FutilityDesigns/Glyph-Reader/Firmware/images/dark.bmp

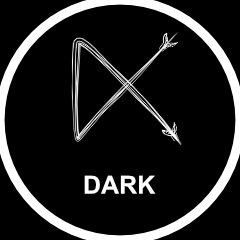
Firmware/images/dark.bmp
