FutilityDesigns/Glyph-Reader/Firmware/images/Gust.bmp

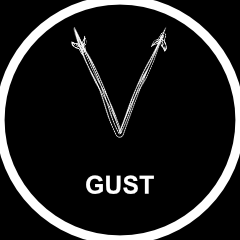
Firmware/images/Gust.bmp
