FutilityDesigns/Glyph-Reader/Firmware/images/halt.bmp

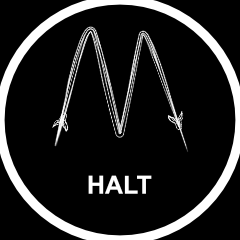
Firmware/images/halt.bmp
