FutilityDesigns/Glyph-Reader/Firmware/images/ignite.bmp

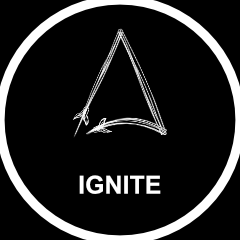
Firmware/images/ignite.bmp
