FutilityDesigns/Glyph-Reader/Firmware/images/lower.bmp

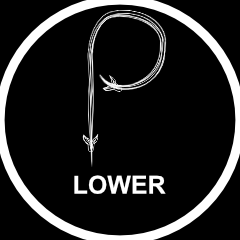
Firmware/images/lower.bmp
