FutilityDesigns/Glyph-Reader/Firmware/images/raise.bmp

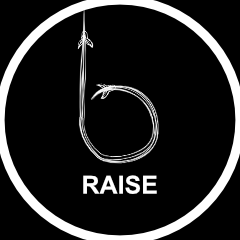
Firmware/images/raise.bmp
