FutilityDesigns/Glyph-Reader/Firmware/images/unlock.bmp

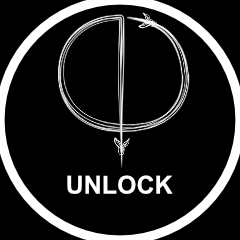
Firmware/images/unlock.bmp
