FutilityDesigns/Glyph-Reader/Spell Cheat Sheet.jpg

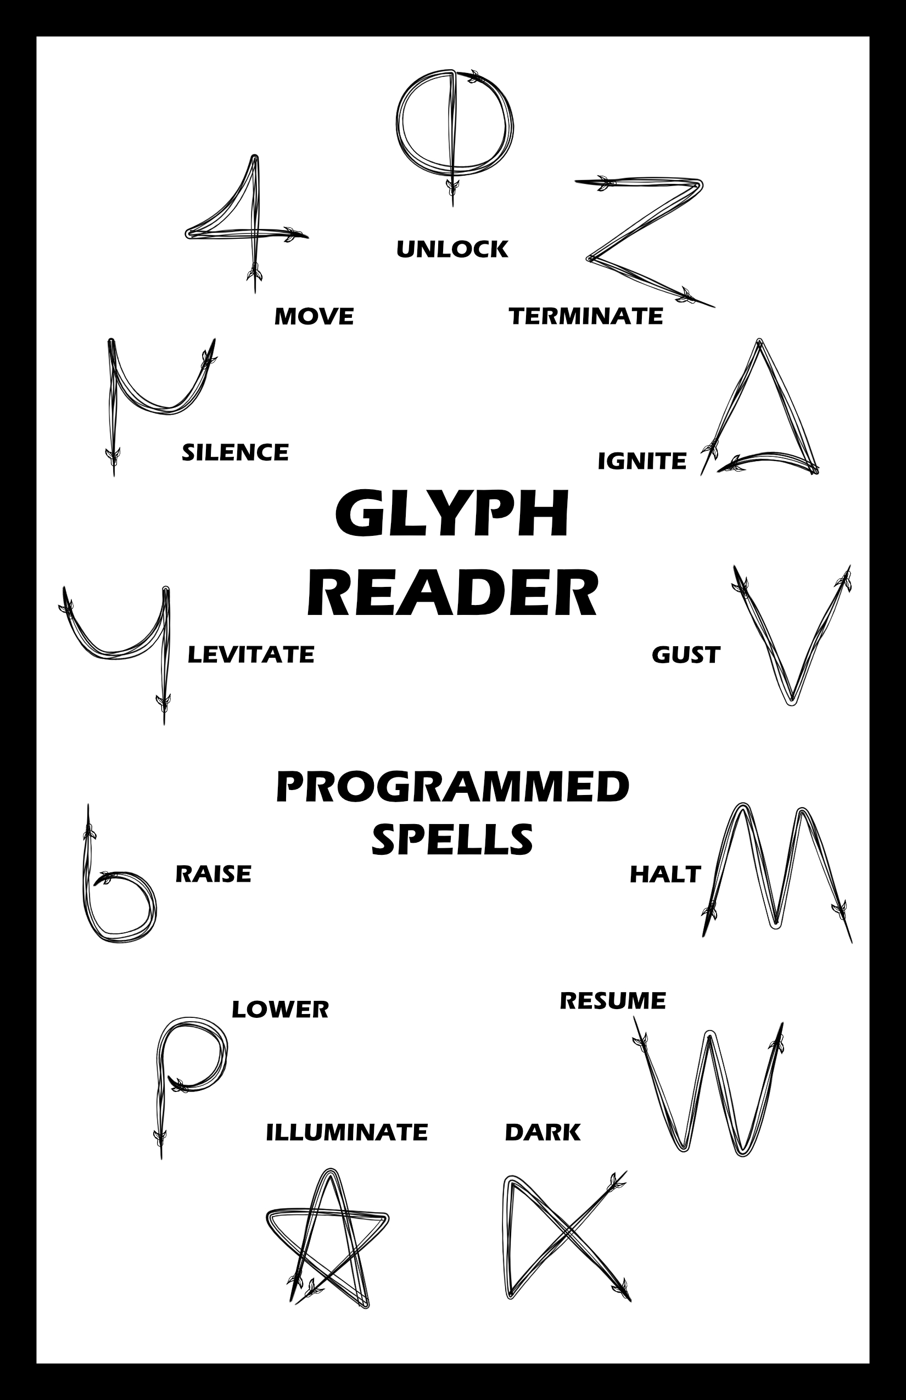
Spell Cheat Sheet.jpg
