FutilityDesigns/Glyph-Reader/Firmware/src/screenFunctions.cpp

/**
================================================================================
  Screen Functions - GC9A01A Round LCD Display Implementation
================================================================================
 * 
 * This module manages the 240x240 pixel round LCD display for real-time gesture
 * visualization, spell name display, and visual feedback during wand tracking.
 * 
 * HARDWARE:
 * - Display: GC9A01A 240x240 round LCD (1.28" diameter)
 * - Interface: SPI (separate bus from SD card)
 * - Backlight: GPIO controlled PWM (manual on/off, no dimming currently)
 * 
 * COORDINATE SYSTEMS:
 * - Camera: 0-1023 x 0-1023 (Pixart IR sensor raw coordinates)
 * - Display: 0-239 x 0-239 (LCD pixel coordinates)
 * - Pattern: 0-1000 x 0-1000 (normalized spell pattern space)
 * All coordinate mappings use Arduino map() function for scaling.
 * 
 * POWER MANAGEMENT:
 * - Backlight timeout controlled by global screenOnTime variable
 * 
 * IMAGE SUPPORT:
 * - Loads 24-bit BMP files from SD card for custom spell images
 * - Converts BMP (BGR) to RGB565 display format on-the-fly
 * - Handles bottom-to-top BMP row order reversal
 * - Falls back to text display if image load fails
 */

#include "screenFunctions.h"
#include "glyphReader.h"
#include "sdFunctions.h"
#include "spell_patterns.h"
#include "spell_matching.h"
#include <Fonts/FreeSansBold18pt7b.h>
#include <Fonts/FreeSansBold24pt7b.h>
#include <Fonts/FreeSansBold12pt7b.h>

//=====================================
// Global Display Object
//=====================================

/// GC9A01A display controller instance
/// Configured with SPI pins: CS=10, DC=9, RST=8
Adafruit_GC9A01A tft(TFT_CS, TFT_DC, TFT_RST);

//=====================================
// IR Trail Tracking State
//=====================================

/// Last drawn IR point X coordinate (display space: 0-239)
/// -1 indicates no previous point (trail start/reset)
static int lastIRX = -1;

/// Last drawn IR point Y coordinate (display space: 0-239)
/// -1 indicates no previous point (trail start/reset)
static int lastIRY = -1;

//=====================================
// Spell Image Color System
//=====================================

/**
 * User-customizable primary color for spell images (RGB565 format)
 * Applied to grayscale regions in BMP files via lookup table.
 * Default: White (0xFFFF) until user selects a color in settings.
 */
static uint16_t spellPrimaryColorRGB565 = 0xFFFF;

/**
 * User-customizable accent color for spell images (RGB565 format)
 * Applied to lime green (0,255,0) placeholder pixels in BMP files.
 * Default: Yellow (0xFFE0)
 */
static uint16_t spellAccentColorRGB565 = 0xFFE0;

/**
 * Grayscale-to-tinted-color lookup table (256 entries)
 * Maps grayscale intensity (0-255) to RGB565 color tinted toward primary color.
 * Pre-computed when setSpellImageColors() is called for fast BMP rendering.
 * Index 0 = black, Index 255 = full primary color.
 */
static uint16_t primaryLUT[256];

/// Flag indicating if primaryLUT has been initialized
static bool primaryLUTInitialized = false;

//=====================================
// Predefined Color Palette
//=====================================

/**
 * Predefined spell color palette in RGB888 format
 * These colors are available in the settings color picker.
 * White is first so device defaults to white until user picks a color.
 * Colors are converted to RGB565 on first use via ensurePredefinedColorsInit().
 */
static const uint8_t predefinedRGB888[][3] = {
  {255, 255, 255}, // White (default)
  {255, 0, 0},     // Red
  {255, 127, 0},   // Orange
  {255, 255, 0},   // Yellow
  {0, 255, 0},     // Green
  {0, 255, 255},   // Cyan
  {0, 0, 255},     // Blue
  {149, 0, 255},   // Indigo
  {255, 0, 228}    // Magenta
};

/// Number of concrete colors in predefinedRGB888 array
static const int PREDEFINED_COLOR_COUNT = sizeof(predefinedRGB888) / sizeof(predefinedRGB888[0]);

/// Predefined colors converted to RGB565 format (populated lazily)
static uint16_t predefinedRGB565[PREDEFINED_COLOR_COUNT];

/// Flag indicating if predefinedRGB565 array has been initialized
static bool predefinedColorsInit = false;

/**
 * Virtual index representing "Random" color mode in the picker
 * When selected, a random color from the palette is chosen each time
 * a spell is displayed. Not stored in predefinedRGB565 array.
 */
static const int RANDOM_COLOR_INDEX = PREDEFINED_COLOR_COUNT;

/// Flag indicating if random color mode is active
/// When true, spell display picks a random predefined color each time
static bool randomColorMode = false;

//=====================================
// Forward Declarations
//=====================================

/// Pack RGB888 components into RGB565 format
static inline uint16_t packRGB565(uint8_t r, uint8_t g, uint8_t b);

/// Draw a rainbow gradient swatch (used by color picker for "Random" option)
static void drawRainbowSwatch(int sx, int sy, int sw, int sh);

//=====================================
// Color Palette Initialization
//=====================================

/**
 * Initialize predefined color palette (lazy initialization)
 * Converts RGB888 colors to RGB565 format on first call.
 * Safe to call multiple times - only initializes once.
 */
static void ensurePredefinedColorsInit() {
  if (predefinedColorsInit) return;
  for (int i = 0; i < PREDEFINED_COLOR_COUNT; ++i) {
    predefinedRGB565[i] = packRGB565(predefinedRGB888[i][0], predefinedRGB888[i][1], predefinedRGB888[i][2]);
  }
  predefinedColorsInit = true;
}

/**
 * Set spell primary color by palette index
 * Called when user selects a color in the settings menu.
 * 
 * param index: Index into predefined color palette (0 to PREDEFINED_COLOR_COUNT-1)
 *              If index >= PREDEFINED_COLOR_COUNT, enables random color mode
 *              If index < 0, function returns without changes
 * 
 * When random mode is enabled, a new random color is picked each time
 * a spell is displayed (in displaySpellName function).
 */
void setSpellPrimaryColorByIndex(int index) {
  ensurePredefinedColorsInit();
  if (index < 0) return;
  if (index >= PREDEFINED_COLOR_COUNT) {
    // Random mode selected
    randomColorMode = true;
    return;
  }
  randomColorMode = false;
  setSpellImageColors(predefinedRGB565[index], spellAccentColorRGB565);
}

/**
 * Get RGB565 color value from predefined palette by index
 * 
 * param index: Palette index (0 to PREDEFINED_COLOR_COUNT-1)
 * return RGB565 color value, or:
 *         - 0x0000 (black) if index < 0
 *         - 0xFFFF (white) if index >= PREDEFINED_COLOR_COUNT (e.g., RANDOM_COLOR_INDEX)
 */
uint16_t getPredefinedColor(int index) {
  ensurePredefinedColorsInit();
  if (index < 0) return 0x0000;
  if (index < PREDEFINED_COLOR_COUNT) return predefinedRGB565[index];
  // RANDOM_COLOR_INDEX or out-of-range -> return white as placeholder
  return 0xFFFF;
}

/**
 * Get total number of color options in the picker (including Random)
 * 
 * return PREDEFINED_COLOR_COUNT + 1 (concrete colors plus Random option)
 */
int getPredefinedColorCount() {
  // Expose one extra slot for the "Random" option
  return PREDEFINED_COLOR_COUNT + 1;
}

/**
 * Check if random color mode is currently active
 * Used by other modules to determine if the Random slot should be highlighted
 * in the color picker UI.
 * 
 * return true if random mode is active, false if a specific color is selected
 */
bool isRandomColorMode() {
  return randomColorMode;
}

//=====================================
// Color Picker UI
//=====================================

/**
 * Display color picker screen for spell color selection
 * Shows a grid of color swatches with the selected one highlighted.
 * The last swatch is a rainbow gradient representing "Random" mode.
 * 
 * param selectedIndex: Currently selected color index (0 to getPredefinedColorCount()-1)
 * 
 * UI Layout:
 * - Title "Spell Color" at top (centered)
 * - Two rows of color swatches (36x36 pixels each, 8px gap)
 * - Selected swatch has double white border
 * - Instructions at bottom: "BTN1: Select  BTN2: Next"
 */
void displayColorPicker(int selectedIndex) {
  ensurePredefinedColorsInit();
  // Clear area and draw title
  tft.fillScreen(0x0000);
  tft.setFont(&FreeSansBold12pt7b);
  tft.setTextColor(0xFFFF);
  int16_t x1, y1; uint16_t w, h;
  const char* title = "Spell Color";
  tft.getTextBounds(title, 0, 0, &x1, &y1, &w, &h);
  tft.setCursor((240 - w) / 2, 20 + h);
  tft.println(title);
  tft.setFont();

  // Draw swatches in up to two centered rows so all swatches fit on screen
  const int swatchSize = 36;
  const int gap = 8;
  // Split into two rows: compute columns per row (ceil(count/2))
  int totalCount = getPredefinedColorCount();
  int cols = (totalCount + 1) / 2;
  int rows = (totalCount + cols - 1) / cols; // should be 1 or 2
  int totalWidth = cols * swatchSize + (cols - 1) * gap;
  int startX = (240 - totalWidth) / 2;
  int rowY1 = 70;
  int rowY2 = rowY1 + swatchSize + 12;
  for (int i = 0; i < totalCount; ++i) {
    int row = i / cols;
    int col = i % cols;
    int sx = startX + col * (swatchSize + gap);
    int sy = (row == 0) ? rowY1 : rowY2;
    // Draw swatch background (border)
    tft.drawRect(sx - 2, sy - 2, swatchSize + 4, swatchSize + 4, 0xFFFF);
    // Fill color or draw Random label
    if (i == RANDOM_COLOR_INDEX) {
      drawRainbowSwatch(sx, sy, swatchSize, swatchSize);
    } else {
      tft.fillRect(sx, sy, swatchSize, swatchSize, predefinedRGB565[i]);
    }
    // Highlight selection
    if (i == selectedIndex) {
      tft.drawRect(sx - 4, sy - 4, swatchSize + 8, swatchSize + 8, 0xFFFF);
    }
  }

  // Instructions
  tft.setTextSize(1);
  tft.setTextColor(0x7BEF);
  const char* inst1 = "BTN1: Select  BTN2: Next";
  tft.getTextBounds(inst1, 0, 0, &x1, &y1, &w, &h);
  tft.setCursor((240 - w) / 2, rowY2 + swatchSize + 16);
  tft.print(inst1);

  screenOnTime = millis();
}

//=====================================
// Color Conversion Helpers
//=====================================

/**
 * Pack 8-bit RGB components into RGB565 format
 * RGB565 packs 16 bits of color: 5 bits red, 6 bits green, 5 bits blue.
 * Human eyes are more sensitive to green, hence the extra bit.
 * 
 * param r: Red component (0-255)
 * param g: Green component (0-255)
 * param b: Blue component (0-255)
 * return Packed RGB565 value (16-bit)
 * 
 * Bit layout: RRRRRGGG GGGBBBBB
 */
static inline uint16_t packRGB565(uint8_t r, uint8_t g, uint8_t b) {
  return ((r & 0xF8) << 8) | ((g & 0xFC) << 3) | (b >> 3);
}

/**
 * Draw a rainbow gradient swatch for the "Random" color option
 * Divides the swatch area into vertical stripes, one for each predefined color.
 * 
 * param sx: Swatch X position (top-left corner)
 * param sy: Swatch Y position (top-left corner)
 * param sw: Swatch width in pixels
 * param sh: Swatch height in pixels
 */
static void drawRainbowSwatch(int sx, int sy, int sw, int sh) {
  ensurePredefinedColorsInit();
  int n = PREDEFINED_COLOR_COUNT;
  if (n <= 0) return;
  int stripe = sw / n;
  for (int i = 0; i < n; ++i) {
    int x = sx + i * stripe;
    int w = (i == n - 1) ? (sw - stripe * (n - 1)) : stripe;
    tft.fillRect(x, sy, w, sh, predefinedRGB565[i]);
  }
}

//=====================================
// BMP Placeholder Color Definitions
//=====================================

/**
 * Placeholder colors for BMP image recoloring system
 * 
 * Artists creating spell images should use these specific RGB values
 * to mark regions that will be dynamically recolored at runtime:
 * 
 * PRIMARY PLACEHOLDER: Magenta (255, 0, 255)
 *   - Used for main spell effect areas
 *   - Replaced with user's selected spell color
 *   - Grayscale variants (R==G==B) are also tinted toward primary color
 * 
 * ACCENT PLACEHOLDER: Lime Green (0, 255, 0)
 *   - Used for secondary/accent details
 *   - Replaced with accent color (currently yellow)
 * 
 * Pure black (0, 0, 0) is preserved as-is for backgrounds.
 */
static const uint8_t PLACEHOLDER_PRIMARY_R = 255; // Magenta (R=255,G=0,B=255)
static const uint8_t PLACEHOLDER_PRIMARY_G = 0;
static const uint8_t PLACEHOLDER_PRIMARY_B = 255;

static const uint8_t PLACEHOLDER_ACCENT_R = 0;   // Lime green (R=0,G=255,B=0)
static const uint8_t PLACEHOLDER_ACCENT_G = 255;
static const uint8_t PLACEHOLDER_ACCENT_B = 0;

//=====================================
// Display Initialization
//=====================================

/**
 * Initialize GC9A01A round display and backlight
 * Sets up SPI bus, initializes display controller, configures backlight GPIO,
 * and displays a startup animation (random color flash + reference circle).
 * 
 * INITIALIZATION SEQUENCE:
 * 1. Configure SPI bus with correct pins (separate bus from SD card)
 * 2. Call tft.begin() to initialize GC9A01A controller
 * 3. Set up backlight GPIO as output, turn on
 * 4. Set rotation to 0 (portrait, can be 0-3 for different orientations)
 * 5. Flash random color briefly (visual confirmation of successful init)
 * 6. Draw dark gray reference circle at display edge
 * BACKLIGHT CONTROL:
 * - TFT_BL GPIO set HIGH to enable backlight
 * - Manual on/off control (no PWM dimming implemented)
 * - Power management handled by backlightOn/Off() functions
 * Called once during setup() in main.cpp.
 */
void screenInit() {
  LOG_DEBUG("Initializing GC9A01 Display...");
  
  // Initialize SPI bus (clock, MISO=-1 for write-only, MOSI, CS)
  SPI.begin(TFT_SCLK, -1, TFT_MOSI, TFT_CS);
  
  // Initialize the display controller
  LOG_DEBUG("Calling tft.begin()...");
  tft.begin();  // Sends initialization commands to GC9A01A
  LOG_DEBUG("Display initialized!");
  
  delay(100);  // Allow controller to stabilize
  
  // Configure Backlight pin for manual on/off control
  pinMode(TFT_BL, OUTPUT);
  // Use centralized backlight control to ensure consistent polarity
  backlightOn();
  LOG_DEBUG("Backlight pin %d initialized via backlightOn()", TFT_BL);
  delay(100);
#ifdef INVERT_DISPLAY
    tft.setRotation(2);  // Rotate 180 degrees for inverted wiring
#else
  tft.setRotation(0);  // 0-3 for different orientations (0=portrait)
#endif
  
  // Fill screen with random color as visual confirmation (using ESP32 hardware RNG)
  uint16_t randomColor = esp_random() & 0xFFFF;  // Random RGB565 color
  tft.fillScreen(randomColor);
  delay(500);  // Show random color briefly for visual feedback
  
  // Draw outer circle as reference frame for round 240x240 display
  tft.drawCircle(120, 120, 119, 0x4208);  // Center at (120,120), radius 119, dark gray
  
  LOG_DEBUG("Display initialized successfully!");
}

/**
 * Display setup progress messages during boot
 * line: Line number (0-based) for vertical positioning
 * function: Name of subsystem being initialized
 * status: Status string: "init" for in-progress, or result (e.g., "OK", "FAIL")
 * Allows user to see progress and identify failures during boot.
 * USAGE EXAMPLE:
 *   updateSetupDisplay(0, "WiFi", "init");     // Shows "WiFi..."
 *   updateSetupDisplay(0, "WiFi", "OK");       // Shows "WiFi... OK"
 * Called from main.cpp setup() for each initialization step.
 */
void updateSetupDisplay(int line, const String &function, const String &status) {
    // Calculate cursor position based on line number
    tft.setTextSize(1);  // Small text for compact status display
    tft.setTextColor(0xFFFF);  // White color for good contrast
    tft.setCursor(50, line * 10 + 40);  // Vertical spacing, offset from top
    
    if (status == "init") {
      tft.print(function + "...");  // In-progress indicator
    } else {
      tft.print(function + "... " + status);  // Show result (OK/FAIL/etc)
    }
}

/**
 * Draw IR tracking point on display with connected trail
 * x: Camera X coordinate (0-1023 from Pixart IR sensor)
 * y: Camera Y coordinate (0-1023 from Pixart IR sensor)
 * isActive: True if IR point is currently detected, false otherwise
 * Visualizes real-time wand position during gesture recording.
 * Draws green connecting lines between points to show trajectory.
 * COORDINATE MAPPING:
 * - Input: 0-1023 (camera coordinates)
 * - Output: 0-239 (display coordinates)
 * - Uses Arduino map() function for scaling
 * CLEARING BEHAVIOR:
 * - When isActive=false, erases last point (fills with black)
 * - Resets tracking state to allow fresh trail on next gesture
 * Called from main loop during RECORDING state
 */
void drawIRPoint(int x, int y, bool isActive) {
  if (isActive && x >= 0 && y >= 0) {
    // Scale from camera coordinates (0-1023) to display (0-239)
    int displayX = map(x, 0, 1023, 0, 239);
    int displayY = map(y, 0, 1023, 0, 239);
    
    // Draw trail line from previous point to current point
    if (lastIRX >= 0 && lastIRY >= 0) {
      tft.drawLine(lastIRX, lastIRY, displayX, displayY, 0x07E0);  // Green trail
    }
    
    // Draw current point with two-color style for visibility
    tft.fillCircle(displayX, displayY, 5, 0xFFE0);  // Yellow center (bright)
    tft.drawCircle(displayX, displayY, 6, 0xF800);  // Red outline (contrast)
    
    // Update last position for next frame's trail line
    lastIRX = displayX;
    lastIRY = displayY;
  } else {
    // No active IR point - clear last point if it exists
    if (lastIRX >= 0 && lastIRY >= 0) {
      tft.fillCircle(lastIRX, lastIRY, 6, 0x0000);  // Black (erase)
    }
    lastIRX = -1;  // Reset state
    lastIRY = -1;
  }
}

/**
 * Clear IR trail state
 */
void clearIRTrail() {
  lastIRX = -1;
  lastIRY = -1;
}

/**
 * Show ready-state background
 * Fill screen with green and draw border circle to match idle frame.
 */
void showReadyBackground() {
  // Draw a thick green border ring by drawing concentric circle outlines
  // so the center is never fully filled with green (avoids visible flicker).
  const uint16_t GREEN = 0x07E0; // RGB565 green
  const uint16_t BLACK = 0x0000;
  const int cx = 120;
  const int cy = 120;
  const int outerR = 119;
  const int borderThickness = 12; // px, adjust for thicker/thinner ring
  const int innerR = outerR - borderThickness;

  // Start with black background so we never show a full green fill
  tft.fillScreen(BLACK);

  // Draw concentric outlines to form a solid-looking ring without filling
  for (int r = innerR + 1; r <= outerR; r++) {
    tft.drawCircle(cx, cy, r, GREEN);
  }

  // Redraw the reference outer outline for consistency
  tft.drawCircle(cx, cy, outerR, 0x4208);

  screenOnTime = millis();
}


/**
 * Display recognized spell name (image or text)
 * spellName: Null-terminated string containing spell name (e.g., "Illuminate")
 * Shows spell on display when match is found. Tries to load BMP image from SD
 * card first, falls back to centered text if no image or load fails.
 * IMAGE MODE:
 * - Checks hasSpellImage() to see if spell has associated BMP file
 * - Gets filename from getSpellImageFilename() (custom or default naming)
 * - Displays 240x240 BMP centered at (0,0) if load successful
 * - Falls back to text mode if image load fails
 * TEXT MODE:
 * - Purple decorative double circle (radius 110 and 105)
 * - Cyan text (0x07FF), size 3 for readability
 * - Multi-word spells split into two centered lines (10px gap)
 * - Single-word spells centered vertically and horizontally
 * - Uses getTextBounds() for precise centering
 * TIMEOUT MANAGEMENT:
 * - Sets screenSpellOnTime = millis() to start display timeout
 * - Sets screenOnTime = millis() to keep backlight on
 * - Display cleared after timeout (handled in main loop)
 */
void displaySpellName(const char* spellName) {
  // Clear screen to black
  tft.fillScreen(0x0000);
  
  // Check if there's a BMP image for this spell on SD card
  if (hasSpellImage(spellName)) {
    // Get the appropriate filename (custom or default naming convention)
    String filename = getSpellImageFilename(spellName);
    
    Serial.printf("Displaying image for spell: %s\n", filename.c_str());
    
    // Try to display the image centered on screen (0, 0 for 240x240 image)
    // If user preference is Random, pick a random predefined color for this display
    if (randomColorMode) {
      ensurePredefinedColorsInit();
      int r = (int)(esp_random() % PREDEFINED_COLOR_COUNT);
      setSpellImageColors(predefinedRGB565[r], spellAccentColorRGB565);
    }
    if (displayImageFromSD(filename.c_str(), 0, 0)) {
      // Image displayed successfully - set timeouts and return
      screenSpellOnTime = millis();
      screenOnTime = millis();
      return;
    } else {
      // Image failed to load, fall through to text display
      Serial.println("Failed to load image, falling back to text");
      tft.fillScreen(0x0000);  // Clear any partial image artifacts
    }
  }
  
  // TEXT MODE: Draw decorative circle frame
  tft.drawCircle(120, 120, 110, 0x780F);  // Purple outer circle
  tft.drawCircle(120, 120, 105, 0x780F);  // Purple inner circle (double border)
  
  tft.setFont(&FreeSansBold12pt7b);  // Use smooth FreeSansBold font
  tft.setTextColor(0x07FF);  // Cyan color for good contrast
  
  // Check if spell name has a space (indicates multi-word spell)
  String spell = String(spellName);
  int spaceIndex = spell.indexOf(' ');
  
  if (spaceIndex > 0) {
    // Multi-word spell - split into two lines for better fit
    String firstWord = spell.substring(0, spaceIndex);
    String secondWord = spell.substring(spaceIndex + 1);
    
    // Get text bounds for each word to calculate centering
    int16_t x1, y1;
    uint16_t w1, h1, w2, h2;
    tft.getTextBounds(firstWord.c_str(), 0, 0, &x1, &y1, &w1, &h1);
    tft.getTextBounds(secondWord.c_str(), 0, 0, &x1, &y1, &w2, &h2);
    
    // Calculate vertical spacing (total height of both lines + 10px gap)
    int totalHeight = h1 + h2 + 10;  // 10 pixel gap between lines
    int startY = (240 - totalHeight) / 2;  // Center vertically
    
    // Display first word centered horizontally
    // Note: Custom fonts use baseline positioning, so add height to y position
    int centerX1 = (240 - w1) / 2;
    tft.setCursor(centerX1, startY + h1);
    tft.println(firstWord);
    
    // Display second word centered below first
    int centerX2 = (240 - w2) / 2;
    tft.setCursor(centerX2, startY + h1 + h2 + 10);
    tft.println(secondWord);
    
  } else {
    // Single word - center it both horizontally and vertically
    int16_t x1, y1;
    uint16_t w, h;
    tft.getTextBounds(spellName, 0, 0, &x1, &y1, &w, &h);
    
    int centerX = (240 - w) / 2;  // Horizontal center
    int centerY = (240 - h) / 2 + h;  // Vertical center (add h for baseline positioning)
    
    tft.setCursor(centerX, centerY);
    tft.println(spellName);
  }
  
  // Reset to default font for other displays
  tft.setFont();
  
  // Set timeout timers to keep display on for spell viewing
  screenSpellOnTime = millis();  // Spell-specific timeout
  screenOnTime = millis();  // Reset overall screen timeout as well
}

/**
 * Clear display and redraw reference circle
 * Resets display to idle state: black background with dark gray border circle.
 * Also resets IR tracking state to start fresh trail on next gesture.
 * Called when:
 * - Spell display timeout expires
 * - Transitioning from RECORDING back to WAITING_FOR_IR state
 * - User manually clears display
 */
void clearDisplay() {
  tft.fillScreen(0x0000);  // Fill entire display with black
  tft.drawCircle(120, 120, 119, 0x4208);  // Redraw dark gray border circle
  lastIRX = -1;  // Reset IR trail tracking
  lastIRY = -1;
}

/**
 * Turn off display backlight to save power
 * Sets backlight GPIO LOW to disable LED backlight.
 * Also clears screen to black to prevent burn-in.
 */
void backlightOff() {
    // Clear screen to black to prevent burn-in while backlight is off
    tft.fillScreen(0x0000);  // Black
    
#ifdef INVERT_BACKLIGHT
    digitalWrite(TFT_BL, LOW);  // Turn off backlight LED
    LOG_DEBUG("Backlight turned OFF (pin %d set to LOW)", TFT_BL);
#else
    digitalWrite(TFT_BL, HIGH);  // Turn off backlight LED
    LOG_DEBUG("Backlight turned OFF (pin %d set to HIGH)", TFT_BL);
#endif
    backlightStateOn = false;  // Update global state flag
}

/**
 * Turn on display backlight
 * Sets backlight GPIO HIGH to enable LED backlight.
 */
void backlightOn() {
#ifdef INVERT_BACKLIGHT
    digitalWrite(TFT_BL, HIGH);  // Turn on backlight LED
    LOG_DEBUG("Backlight turned ON (pin %d set to HIGH)", TFT_BL);
#else
    digitalWrite(TFT_BL, LOW);  // Turn on backlight LED
    LOG_DEBUG("Backlight turned ON (pin %d set to LOW)", TFT_BL);
#endif
    backlightStateOn = true;  // Update global state flag
}

/**
 * Set the user-preferred colors for spell images.
 * Artists should draw recolorable regions using the placeholder colors
 * (magenta for primary, lime for accent). Those pixels will be replaced
 * with these RGB565 values at display time.
 */
void setSpellImageColors(uint16_t primaryColorRGB565, uint16_t accentColorRGB565) {
  spellPrimaryColorRGB565 = primaryColorRGB565;
  spellAccentColorRGB565 = accentColorRGB565;

  // Reconstruct approximate 8-bit RGB components from RGB565 primary color
  uint8_t p_r = (uint8_t)(((spellPrimaryColorRGB565 >> 11) & 0x1F) << 3);
  uint8_t p_g = (uint8_t)(((spellPrimaryColorRGB565 >> 5) & 0x3F) << 2);
  uint8_t p_b = (uint8_t)((spellPrimaryColorRGB565 & 0x1F) << 3);

  // Build LUT: map grayscale intensity to tinted color scaled by intensity
  for (int i = 0; i < 256; i++) {
    uint8_t r = (uint8_t)((p_r * i + 127) / 255);
    uint8_t g = (uint8_t)((p_g * i + 127) / 255);
    uint8_t b = (uint8_t)((p_b * i + 127) / 255);
    primaryLUT[i] = packRGB565(r, g, b);
  }
  primaryLUTInitialized = true;
}

uint16_t getSpellPrimaryColor() {
  return spellPrimaryColorRGB565;
}

uint16_t getSpellAccentColor() {
  return spellAccentColorRGB565;
}

/**
 * Load and display BMP image from SD card
 * filename: Path to BMP file on SD card (e.g., "/lumos.bmp")
 * x: X coordinate for top-left corner of image on display
 * y: Y coordinate for top-left corner of image on display
 * return true if image displayed successfully, false on error
 * Loads 24-bit uncompressed BMP files from SD card and displays on screen.
 * Handles BMP format quirks: BGR color order, bottom-to-top row storage,
 * and 4-byte row padding.
 * SUPPORTED BMP FORMAT:
 * - Bit depth: 24-bit RGB (8 bits per channel)
 * - Compression: Uncompressed (BI_RGB)
 * - Color order: BGR (Blue-Green-Red)
 * - Row order: Bottom-to-top (BMP standard)
 * - Row padding: Aligned to 4-byte boundaries
 * MEMORY MANAGEMENT:
 * - Allocates heap memory for all rows to avoid SD card seeking
 * - Row buffers: width * sizeof(uint16_t) per row
 * - Total allocation: width * height * 2 bytes (RGB565 format)
 * - Frees all memory before function returns
 * CONVERSION PROCESS:
 * 1. Read BMP header to get width, height, bit depth
 * 2. Validate format (24-bit, uncompressed only)
 * 3. Allocate memory for all rows in RGB565 format
 * 4. Read rows sequentially from file (bottom-to-top in BMP)
 * 5. Convert each pixel from BGR888 to RGB565
 * 6. Write rows to display in reverse order (top-to-bottom)
 * 7. Free all allocated memory 
 * RGB565 CONVERSION:
 * - Red: Top 5 bits of R channel (R & 0xF8) << 8
 * - Green: Top 6 bits of G channel (G & 0xFC) << 3
 * - Blue: Top 5 bits of B channel (B >> 3)
 * USAGE:
 * - Spell images: 240x240 BMP files for full-screen spell display
 * - Custom graphics: Any size BMP can be positioned anywhere on screen
 * 
 * Called from displaySpellName() when spell has associated image file.
 */
bool displayImageFromSD(const char* filename, int16_t x, int16_t y) {
  LOG_DEBUG("Loading image from SD: %s", filename);
  
  // Check if card is present
  if (!isCardPresent()) {
    LOG_DEBUG("No SD card present");
    return false;
  }
  
  // Open file
  File file = openFile(filename, FILE_READ);
  if (!file) {
    LOG_DEBUG("Failed to open file: %s", filename);
    return false;
  }
  
  // Read BMP header
  uint16_t width, height, bitDepth;
  if (!readBMPHeader(file, &width, &height, &bitDepth)) {
    file.close();
    return false;
  }

  // Ensure LUT is built (use current primary color default if user hasn't set one)
  if (!primaryLUTInitialized) {
    setSpellImageColors(spellPrimaryColorRGB565, spellAccentColorRGB565);
  }
  
  // Get the data offset (where pixel data starts)
  uint32_t dataOffset = file.position();
  
  // BMP rows are padded to 4-byte boundaries
  uint16_t rowSize = ((width * 3) + 3) & ~3;
  uint8_t* rowBuffer = (uint8_t*)malloc(rowSize);
  
  if (rowBuffer == NULL) {
    LOG_DEBUG("Failed to allocate row buffer");
    file.close();
    return false;
  }
  
  // Allocate RGB565 buffer for one row
  uint16_t* rgb565Buffer = (uint16_t*)malloc(width * sizeof(uint16_t));
  if (rgb565Buffer == NULL) {
    LOG_DEBUG("Failed to allocate RGB565 buffer");
    free(rowBuffer);
    file.close();
    return false;
  }
  
  // Allocate buffer to hold all rows in memory (so we can reorder without seeking)
  uint16_t** imageRows = (uint16_t**)malloc(height * sizeof(uint16_t*));
  if (imageRows == NULL) {
    LOG_DEBUG("Failed to allocate image rows array");
    free(rgb565Buffer);
    free(rowBuffer);
    file.close();
    return false;
  }
  
  // Allocate memory for each row
  for (int i = 0; i < height; i++) {
    imageRows[i] = (uint16_t*)malloc(width * sizeof(uint16_t));
    if (imageRows[i] == NULL) {
      LOG_DEBUG("Failed to allocate row buffer");
      // Free previously allocated rows
      for (int j = 0; j < i; j++) {
        free(imageRows[j]);
      }
      free(imageRows);
      free(rgb565Buffer);
      free(rowBuffer);
      file.close();
      return false;
    }
  }
  
  // Read all rows sequentially from file (BMP stores bottom-to-top)
  for (int row = 0; row < height; row++) {
    file.read(rowBuffer, rowSize);  // Read one row (with padding)
    
    // Convert each pixel from BGR888 to RGB565 and store in row buffer
    // If the artist used one of the placeholder colors in the BMP
    // (magenta for primary, lime for accent), substitute the
    // user-selected RGB565 color to allow runtime recoloring.
    for (int col = 0; col < width; col++) {
      uint8_t b = rowBuffer[col * 3];      // Blue channel
      uint8_t g = rowBuffer[col * 3 + 1];  // Green channel
      uint8_t r = rowBuffer[col * 3 + 2];  // Red channel

      // Preserve pure black background
      if (r == 0 && g == 0 && b == 0) {
        imageRows[row][col] = 0x0000;
        continue;
      }

      // Accent placeholder (lime: R=0,G=255,B=0) -> flat accent color
      if (r == PLACEHOLDER_ACCENT_R && g == PLACEHOLDER_ACCENT_G && b == PLACEHOLDER_ACCENT_B) {
        imageRows[row][col] = spellAccentColorRGB565;
        continue;
      }

      // If pixel is pure grayscale (R==G==B), tint using LUT (very fast)
      if (r == g && g == b) {
        imageRows[row][col] = primaryLUT[r];
        continue;
      }

      // For any other colored pixel, fall back to direct packing
      imageRows[row][col] = packRGB565(r, g, b);
    }
  }
  
  // Write to display in reverse order (convert BMP bottom-to-top to display top-to-bottom)
  LOG_DEBUG("About to write %dx%d image to display (backlightStateOn=%d)", width, height, backlightStateOn);
  // Ensure backlight is on during the write to rule out transient toggles
  if (!backlightStateOn) {
    LOG_DEBUG("Forcing backlight on for image write");
    backlightOn();
    delay(10);
  }

  tft.startWrite();  // Begin SPI transaction for bulk write
  tft.setAddrWindow(x, y, width, height);  // Set drawing window

  for (int row = height - 1; row >= 0; row--) {  // Reverse row order
    tft.writePixels(imageRows[row], width);  // Write entire row at once
  }

  tft.endWrite();  // End SPI transaction
  LOG_DEBUG("Finished writing image to display");
  // Small delay to allow any hardware/LED drivers to settle
  delay(20);
  
  // Free all allocated memory (row arrays, pointer array, temp buffers)
  for (int i = 0; i < height; i++) {
    free(imageRows[i]);  // Free each row buffer
  }
  free(imageRows);  // Free row pointer array
  free(rgb565Buffer);  // Free temporary row buffer
  
  free(rowBuffer);  // Free BMP row buffer
  file.close();  // Close SD file
  
  LOG_DEBUG("Successfully displayed image: %s", filename);
  return true;
}

/**
 * Visualize spell pattern on display for debugging
 * name: Spell name to display at top
 * pattern: Vector of normalized Point coordinates (0-1000 range)
 * Debug visualization tool to verify spell pattern definitions are correct.
 * Useful for validating custom spell patterns from spells.json.
 * Called from spell_patterns.cpp initialization to preview patterns.
 */
void visualizeSpellPattern(const char* name, const std::vector<Point>& pattern) {
  if (pattern.empty()) return;  // Nothing to draw
  
  // Clear screen and draw border circle
  tft.fillScreen(0x0000);
  tft.drawCircle(120, 120, 119, 0x4208);  // Dark gray reference circle
  
  // Draw spell name centered at top
  tft.setFont(&FreeSansBold12pt7b);
  tft.setTextColor(0xFFFF);  // White text
  int16_t x1, y1;
  uint16_t w, h;
  tft.getTextBounds(name, 0, 0, &x1, &y1, &w, &h);
  tft.setCursor((240 - w) / 2, 10 + h);  // Center horizontally, baseline positioning
  tft.println(name);
  tft.setFont();  // Reset to default font
  
  // Find bounding box of pattern (patterns should already be 0-1000 normalized)
  // Find bounding box of pattern (patterns should already be 0-1000 normalized)
  int minX = pattern[0].x, maxX = pattern[0].x;
  int minY = pattern[0].y, maxY = pattern[0].y;
  for (const auto& p : pattern) {
    minX = min(minX, p.x);
    maxX = max(maxX, p.x);
    minY = min(minY, p.y);
    maxY = max(maxY, p.y);
  }
  
  // Scale pattern to fit in display with margins
  int displayMargin = 40;  // 40px margin on all sides
  int displaySize = 240 - (displayMargin * 2);  // 160px drawing area
  
  // Draw pattern point by point with connecting lines (animated)
  for (size_t i = 0; i < pattern.size(); i++) {
    // Scale from 0-1000 normalized space to display space (40-200)
    int displayX = map(pattern[i].x, 0, 1000, displayMargin, 240 - displayMargin);
    int displayY = map(pattern[i].y, 0, 1000, displayMargin, 240 - displayMargin);
    
    // Draw connecting line from previous point
    if (i > 0) {
      int prevX = map(pattern[i-1].x, 0, 1000, displayMargin, 240 - displayMargin);
      int prevY = map(pattern[i-1].y, 0, 1000, displayMargin, 240 - displayMargin);
      tft.drawLine(prevX, prevY, displayX, displayY, 0x07E0);  // Green trail line
    }
    
    // Draw point with different colors for start/end/middle
    if (i == 0) {
      // Starting point - larger red circle
      tft.fillCircle(displayX, displayY, 4, 0xF800);  // Red start marker
    } else if (i == pattern.size() - 1) {
      // Ending point - blue circle
      tft.fillCircle(displayX, displayY, 3, 0x001F);  // Blue end marker
    } else {
      // Middle points - small yellow circles
      tft.fillCircle(displayX, displayY, 2, 0xFFE0);  // Yellow trajectory points
    }
    
    delay(30);  // Small delay to animate the drawing (30ms per point)
  }
  
  delay(1200);  // Hold final pattern for 1.2 seconds so user can see it
}

/**
 * Visualize spell match comparison for debugging
 * Overlays the matched spell pattern (green) and user trajectory (cyan)
 * to show how well they align. Used for debugging match accuracy.
 * name: Spell name
 * spellPattern: The matched spell pattern (resampled, normalized)
 * userTrajectory: The user's drawn trajectory (resampled, normalized)
 * similarity: The calculated similarity score (0.0-1.0)
 */
void visualizeMatchComparison(const char* name, const std::vector<Point>& spellPattern, const std::vector<Point>& userTrajectory, float similarity) {
  if (spellPattern.empty() || userTrajectory.empty()) return;
  
  // Clear screen and draw border circle
  tft.fillScreen(0x0000);
  tft.drawCircle(120, 120, 119, 0x4208);  // Dark gray reference circle
  
  // Draw spell name and similarity score at top
  tft.setFont(&FreeSansBold12pt7b);
  tft.setTextColor(0xFFFF);  // White text
  int16_t x1, y1;
  uint16_t w, h;
  
  // Display spell name
  tft.getTextBounds(name, 0, 0, &x1, &y1, &w, &h);
  tft.setCursor((240 - w) / 2, 15 + h);
  tft.println(name);
  
  // Display similarity score
  tft.setFont(&FreeSansBold12pt7b);
  char scoreText[32];
  snprintf(scoreText, sizeof(scoreText), "%.1f%%", similarity * 100);
  tft.getTextBounds(scoreText, 0, 0, &x1, &y1, &w, &h);
  tft.setTextColor(similarity >= MATCH_THRESHOLD ? 0x07E0 : 0xF800);  // Green if match, red if no match
  tft.setCursor((240 - w) / 2, 35 + h);
  tft.println(scoreText);
  tft.setFont();  // Reset font
  
  // Drawing area with margins - scale to 80% and center
  int displayMargin = 55;  // Top margin for text
  int fullDisplaySize = 240 - (displayMargin * 2);  // Full available size
  float scale = 0.8;  // Scale down to 80%
  int scaledSize = fullDisplaySize * scale;  // Actual drawing size
  int centerOffset = (fullDisplaySize - scaledSize) / 2;  // Offset to center
  int leftMargin = displayMargin + centerOffset;
  int rightMargin = 240 - displayMargin - centerOffset;
  int topMargin = displayMargin + centerOffset;
  int bottomMargin = 240 - displayMargin - centerOffset + 55;
  
  // Draw spell pattern (green)
  for (size_t i = 0; i < spellPattern.size(); i++) {
    int displayX = map(spellPattern[i].x, 0, 1000, leftMargin, rightMargin);
    int displayY = map(spellPattern[i].y, 0, 1000, topMargin, bottomMargin);
    
    // Draw connecting line
    if (i > 0) {
      int prevX = map(spellPattern[i-1].x, 0, 1000, leftMargin, rightMargin);
      int prevY = map(spellPattern[i-1].y, 0, 1000, topMargin, bottomMargin);
      tft.drawLine(prevX, prevY, displayX, displayY, 0x07E0);  // Green line
    }
    
    // Draw point
    tft.fillCircle(displayX, displayY, 2, 0x07E0);  // Green dot
  }
  
  // Draw user trajectory (cyan)
  for (size_t i = 0; i < userTrajectory.size(); i++) {
    int displayX = map(userTrajectory[i].x, 0, 1000, leftMargin, rightMargin);
    int displayY = map(userTrajectory[i].y, 0, 1000, topMargin, bottomMargin);
    
    // Draw connecting line
    if (i > 0) {
      int prevX = map(userTrajectory[i-1].x, 0, 1000, leftMargin, rightMargin);
      int prevY = map(userTrajectory[i-1].y, 0, 1000, topMargin, bottomMargin);
      tft.drawLine(prevX, prevY, displayX, displayY, 0x07FF);  // Cyan line
    }
    
    // Draw point
    tft.fillCircle(displayX, displayY, 2, 0x07FF);  // Cyan dot
  }
  
  // Add legend at bottom
  tft.setTextSize(1);
  tft.setTextColor(0x07E0);  // Green
  tft.setCursor(20, 220);
  tft.print("Spell");
  
  tft.setTextColor(0x07FF);  // Cyan
  tft.setCursor(180, 220);
  tft.print("User");
  
  // Set timeout timers
  screenSpellOnTime = millis();
  screenOnTime = millis();
}

//=====================================
// Settings Menu Display
//=====================================

// Number of settings in the menu (set in displaySettingsMenu)
int SETTINGS_MENU_COUNT = 6;

/**
 * Display settings menu on screen
 * Shows the current setting name and value with visual indicators.
 * Displays:
 * - Setting name at top
 * - Current value in center (large text)
 * - Navigation indicators (arrows/brackets)
 * - Edit mode indicator
 * 
 * settingIndex: Which setting to display (0 = NL ON, 1 = NL OFF, 2 = NL RAISE, 3 = NL LOWER)
 * valueIndex: Which value option is selected (0 = Disabled, 1+ = spell index)
 * isEditing: True if currently editing value, false if browsing settings
 */
void displaySettingsMenu(int settingIndex, int valueIndex, bool isEditing) {
    // Clear display
    tft.fillScreen(0x0000);  // Black background
    
    // Define category and setting names
    // Categories: Night Light (0-3), Spells (4-5)
    const char* settingNames[] = {
      "On Spell",
      "Off Spell",
      "Raise Spell",
      "Lower Spell",
      "Add Spell",
      "Spell Color"
    };
    SETTINGS_MENU_COUNT = sizeof(settingNames) / sizeof(settingNames[0]);
    
    // Determine which category this setting belongs to
    const char* categoryName = (settingIndex <= 3) ? "Night Light" : "Spells";
    
    // Get value name based on setting type
    String valueName;
    if (settingIndex == 4) {
        valueName = "Press to Start";
    } else if (valueIndex == 0) {
        valueName = "Disabled";
    } else if (valueIndex > 0 && valueIndex <= (int)spellPatterns.size()) {
        valueName = spellPatterns[valueIndex - 1].name;
    } else {
        valueName = "Error";
    }
    
    // Display category name at top (centered) - FreeSansBold 18pt
    tft.setFont(&FreeSansBold12pt7b);
    tft.setTextColor(0xFFFF);  // White text
    int16_t x1, y1;
    uint16_t w, h;
    
    tft.getTextBounds(categoryName, 0, 0, &x1, &y1, &w, &h);
    int categoryCenterX = (240 - w) / 2;
    tft.setCursor(categoryCenterX, 20 + h);
    tft.println(categoryName);
    
    // Display setting name below category (centered) - FreeSansBold 12pt
    tft.setFont(&FreeSansBold12pt7b);
    if (settingIndex >= 0 && settingIndex < SETTINGS_MENU_COUNT) {
      tft.getTextBounds(settingNames[settingIndex], 0, 0, &x1, &y1, &w, &h);
      int settingCenterX = (240 - w) / 2;
      tft.setCursor(settingCenterX, 45 + h);
      tft.println(settingNames[settingIndex]);
    }
    
    tft.setFont();  // Reset to default font
    
    // Display navigation/edit indicator (centered)
    tft.setTextSize(1);
    if (settingIndex != 4) {  // Not Add Spell (which is action-only)
      if (isEditing) {
        // Editing mode - show brackets around value
        tft.setTextColor(0x07E0);  // Green for edit mode
        String editText = "[ EDITING ]";
        int editWidth = editText.length() * 6;  // Size 1: ~6px per char
        int editCenterX = (240 - editWidth) / 2;
        tft.setCursor(editCenterX, 75);
        tft.print(editText);
      } else {
        // Browse mode - show navigation hint
        tft.setTextColor(0xFFE0);  // Yellow for browse mode
        String browseText = "< BROWSE >";
        int browseWidth = browseText.length() * 6;  // Size 1: ~6px per char
        int browseCenterX = (240 - browseWidth) / 2;
        tft.setCursor(browseCenterX, 75);
        tft.print(browseText);
      }
    }
    
    // Display current value in center (FreeSansBold 24pt)
    tft.setFont(&FreeSansBold12pt7b);
    tft.setTextColor(0xFFFF);  // White text

    if (settingIndex == 5) {
      // Show current color swatch centered
      ensurePredefinedColorsInit();
      int sw = 60; int sh = 60;
      int sx = (240 - sw) / 2;
      int sy = 100;
      // When not editing, derive the current color index from the active primary color
      int colorIndexToShow = valueIndex;
      if (!isEditing) {
        if (randomColorMode) {
          colorIndexToShow = RANDOM_COLOR_INDEX;
        } else {
          uint16_t cur = getSpellPrimaryColor();
          // Find matching predefined color index (exclude RANDOM entry)
          colorIndexToShow = 0;
          for (int i = 0; i < PREDEFINED_COLOR_COUNT; ++i) {
            if (getPredefinedColor(i) == cur) { colorIndexToShow = i; break; }
          }
        }
      }
      tft.drawRect(sx - 2, sy - 2, sw + 4, sh + 4, 0xFFFF);
      if (colorIndexToShow == RANDOM_COLOR_INDEX) {
        drawRainbowSwatch(sx, sy, sw, sh);
      } else {
        uint16_t color = getPredefinedColor(colorIndexToShow);
        tft.fillRect(sx, sy, sw, sh, color);
      }

      // Label under swatch
      tft.getTextBounds("Current Color", 0, 0, &x1, &y1, &w, &h);
      tft.setCursor((240 - w) / 2, sy + sh + 20);
      tft.println("Current Color");
    } else {
      // Get text bounds and center horizontally and vertically
      tft.getTextBounds(valueName.c_str(), 0, 0, &x1, &y1, &w, &h);
      int valueCenterX = (240 - w) / 2;
      int valueCenterY = 120 + (h / 2);  // Center vertically with baseline positioning
      tft.setCursor(valueCenterX, valueCenterY);
      tft.println(valueName);
    }
    
    tft.setFont();  // Reset font
    
    // Display instructions at bottom (centered)
    tft.setTextSize(1);
    tft.setTextColor(0x7BEF);  // Light gray
    
    String instruction1;
    if (settingIndex == 4) {
        // Add Spell has different instructions
        instruction1 = "BTN1: Start Recording";
    } else if (isEditing) {
        instruction1 = "BTN2:Cycle BTN1:Save";
    } else {
        instruction1 = "BTN2:Next BTN1:Edit";
    }
    int inst1Width = instruction1.length() * 6;  // Size 1: ~6px per char
    int inst1CenterX = (240 - inst1Width) / 2;
    tft.setCursor(inst1CenterX, 200);
    tft.print(instruction1);
    
    // Show long-press hint (centered)
    String instruction2 = "Hold BTN2: Exit";
    int inst2Width = instruction2.length() * 6;  // Size 1: ~6px per char
    int inst2CenterX = (240 - inst2Width) / 2;
    tft.setCursor(inst2CenterX, 215);
    tft.print(instruction2);
    
    // Update screen timestamp
    screenOnTime = millis();
}

/**
 * Display a centered error message on screen
 * Shows the message in red with FreeSansBold18pt font
 */
void displayError(const char* message) {
  tft.fillScreen(0x0000);
  tft.setFont(&FreeSansBold12pt7b);
  tft.setTextColor(0xF800);  // Red
  
  // Check if message has a space (indicates multi-line)
  String msg = String(message);
  int spaceIndex = msg.indexOf(' ');
  
  if (spaceIndex > 0) {
    // Split into two lines
    String line1 = msg.substring(0, spaceIndex);
    String line2 = msg.substring(spaceIndex + 1);
    
    int16_t x1, y1;
    uint16_t w, h;
    
    // Display first line
    tft.getTextBounds(line1.c_str(), 0, 0, &x1, &y1, &w, &h);
    tft.setCursor((240 - w) / 2, 100 + h);
    tft.println(line1);
    
    // Display second line
    tft.getTextBounds(line2.c_str(), 0, 0, &x1, &y1, &w, &h);
    tft.setCursor((240 - w) / 2, 140 + h);
    tft.println(line2);
  } else {
    // Single line
    int16_t x1, y1;
    uint16_t w, h;
    tft.getTextBounds(message, 0, 0, &x1, &y1, &w, &h);
    tft.setCursor((240 - w) / 2, 120 + h);
    tft.println(message);
  }
  
  tft.setFont();
}

/**
 * Display a centered message on screen
 * Shows the message in the specified color with FreeSansBold18pt font
 */
void displayMessage(const char* message, uint16_t color) {
  tft.fillScreen(0x0000);
  tft.setFont(&FreeSansBold12pt7b);
  tft.setTextColor(color);
  
  int16_t x1, y1;
  uint16_t w, h;
  tft.getTextBounds(message, 0, 0, &x1, &y1, &w, &h);
  tft.setCursor((240 - w) / 2, 120 + h);
  tft.println(message);
  
  tft.setFont();
}
